sanchosimmy/Wireless-Control/Documentation/latex/globalvariable_8h__incl.pdf

C:/Users/Akshay/workspace
_v6_0/Wireless_Control
/globalvariable.h
stdbool.h | stdint.h
