sanchosimmy/Wireless-Control/Documentation/latex/input_8h__dep__incl.pdf

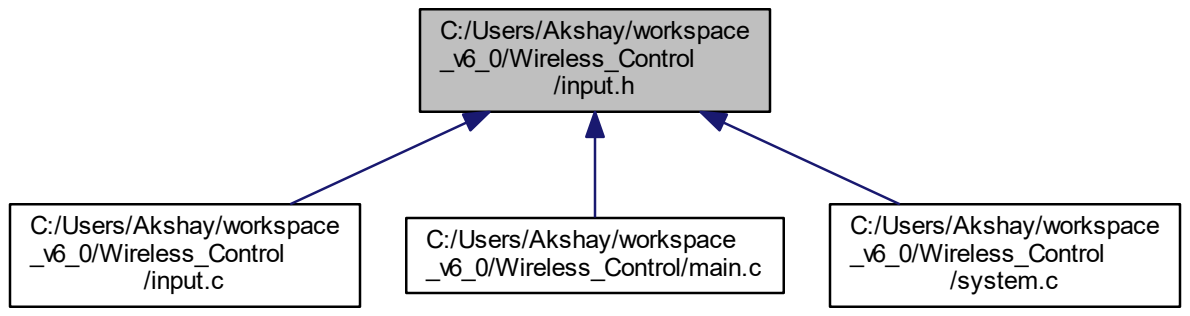
[picture p19: figure]
C:/Users/Akshay/workspace _v6_0/Wireless_Control /input.h; C:/Users/Akshay/workspace _v6_0/Wireless_Control /input.c; C:/Users/Akshay/workspace _v6_0/Wireless_Control/main.c; C:/Users/Akshay/workspace _v6_0/Wireless_Control /system.c
