sanchosimmy/Wireless-Control/Documentation/latex/input_8h__incl.pdf

C:/Users/Akshay/workspace
_v6_0/Wireless_Control
/input.h

stdint.h
