sanchosimmy/Wireless-Control/Documentation/latex/led_8h__dep__incl.pdf

C:/Users/Akshay/workspace
_v6_0/Wireless_Control/led.h

C:/Users/Akshay/workspace
_v6_0/Wireless_Control/led.c

C:/Users/Akshay/workspace
_v6_0/Wireless_Control/main.c
