sanchosimmy/Wireless-Control/Documentation/latex/pinmap_8h__dep__incl.pdf

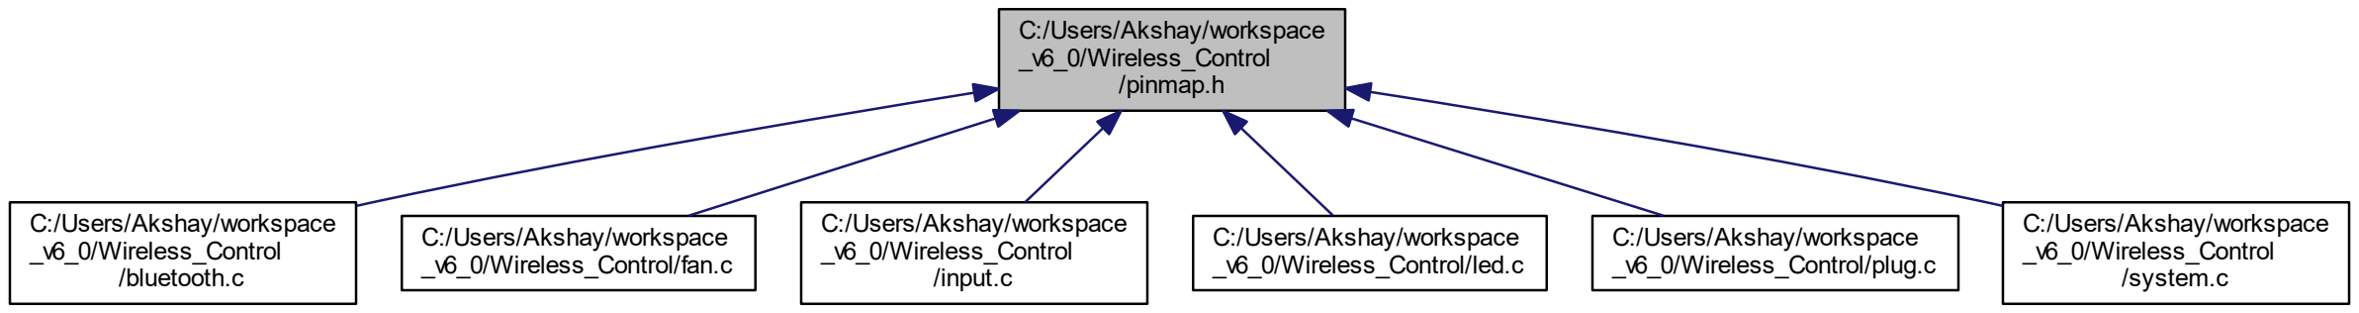
[picture p20: figure]
C:/Users/Akshay/workspace _v6_0/Wireless_Control /pinmap.h; C:/Users/Akshay/workspace _v6_0/Wireless_Control /bluetooth.c; C:/Users/Akshay/workspace _v6_0/Wireless_Control/fan.c; C:/Users/Akshay/workspace _v6_0/Wireless_Control /input.c; C:/Users/Akshay/workspace _v6_0/Wireless_Control/led.c; C:/Users/Akshay/workspace _v6_0/Wireless_Control/plug.c; C:/Users/Akshay/workspace _v6_0/Wireless_Control /system.c
