sanchosimmy/Wireless-Control/Documentation/latex/pinmap_8h__incl.pdf

C:/Users/Akshay/workspace
_v6_0/Wireless_Control
/pinmap.h
stdint.h | stdbool.h | driverlib/gpio.h | driverlib/pin_map.h
