sanchosimmy/Wireless-Control/Documentation/latex/plug_8c__incl.pdf

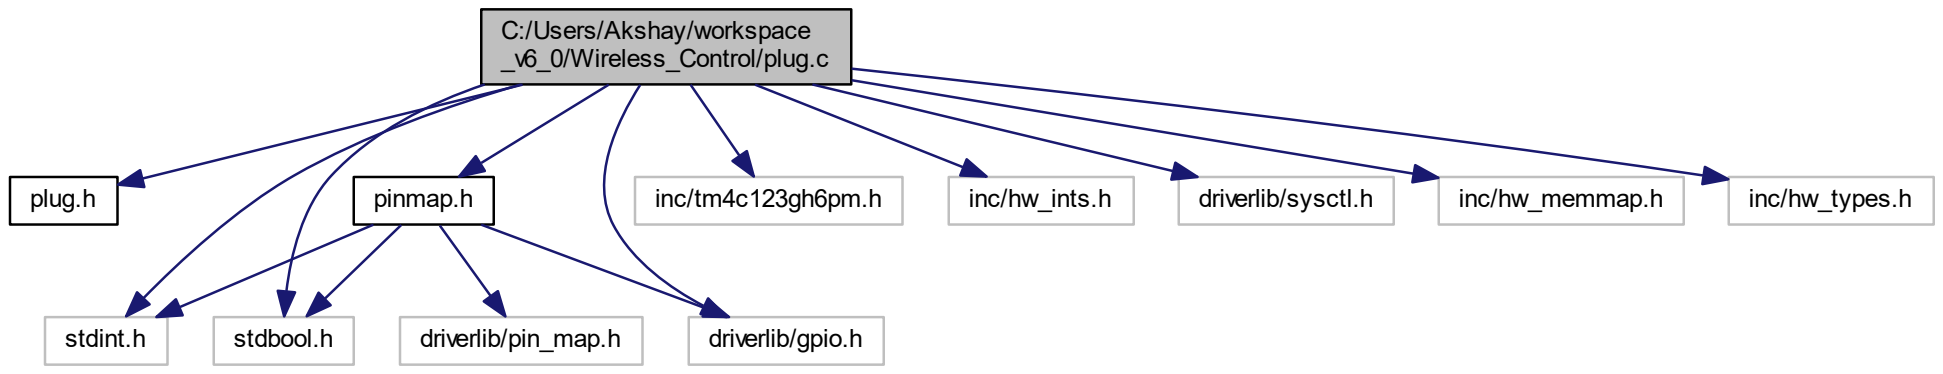
[picture p21: figure]
C:/Users/Akshay/workspace _v6_0/Wireless_Control/plug.c; plug.h; stdint.h; stdbool.h; inc/tm4c123gh6pm.h; inc/hw_ints.h; driverlib/gpio.h; pinmap.h; driverlib/sysctl.h; inc/hw_memmap.h; inc/hw_types.h; driverlib/pin_map.h
