sanchosimmy/Wireless-Control/Documentation/latex/plug_8h__dep__incl.pdf

C:/Users/Akshay/workspace
_v6_0/Wireless_Control/plug.h

C:/Users/Akshay/workspace
_v6_0/Wireless_Control/main.c

C:/Users/Akshay/workspace
_v6_0/Wireless_Control/plug.c
