sanchosimmy/Wireless-Control/Documentation/latex/system_8h__incl.pdf

C:/Users/Akshay/workspace
_v6_0/Wireless_Control
/system.h

stdint.h
