sanchosimmy/Wireless-Control/Hardwear_PCB/bottom_fan - Copy.png

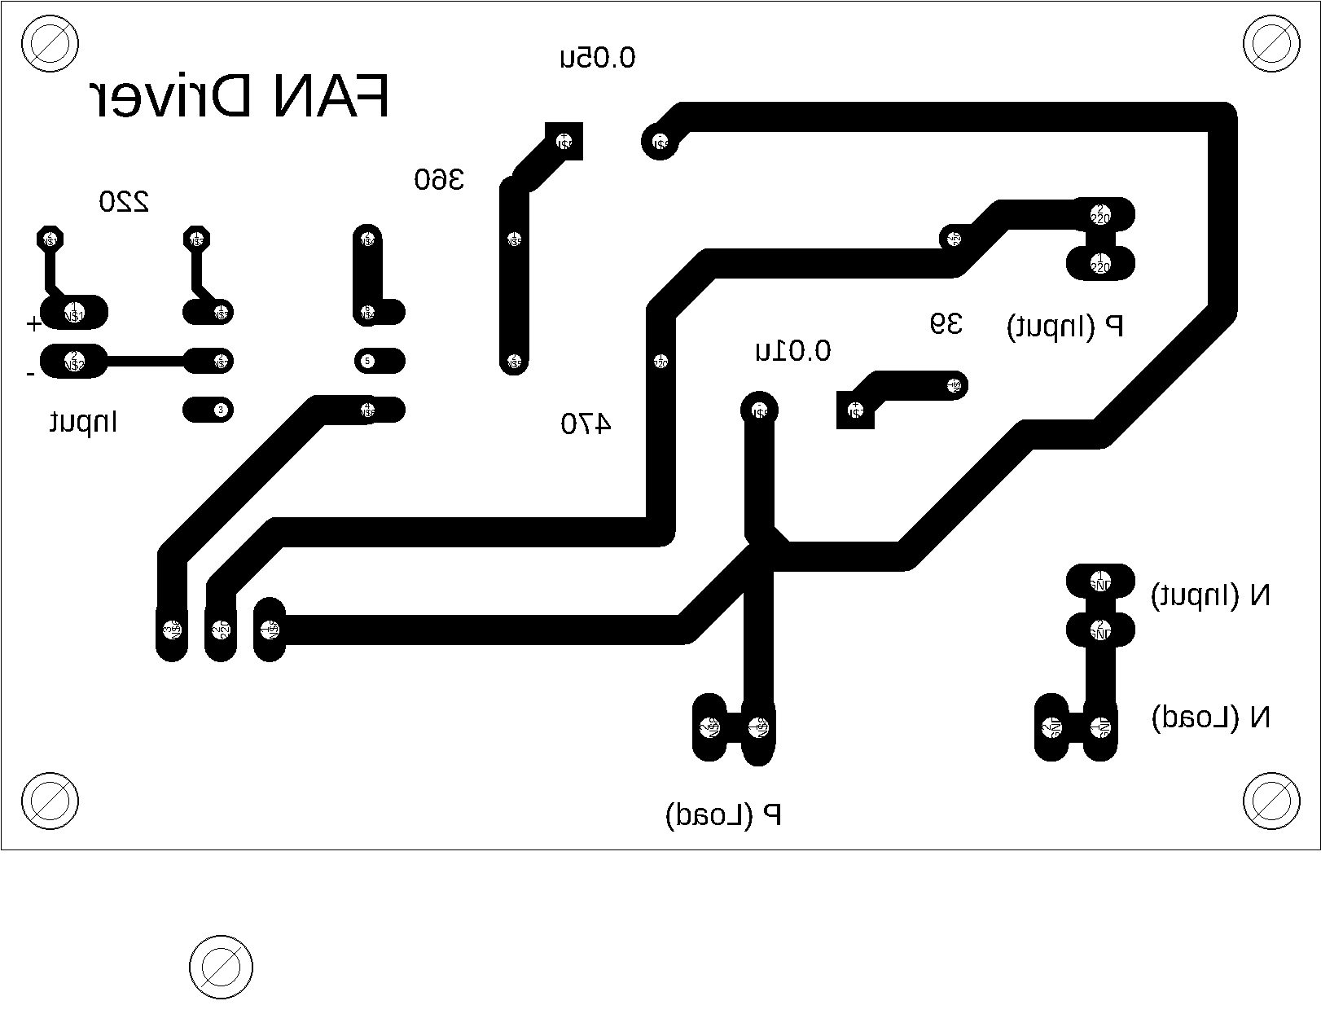
Hardwear_PCB/bottom_fan - Copy.png
