sanchosimmy/Wireless-Control/Hardwear_PCB/bottom_led - Copy.png

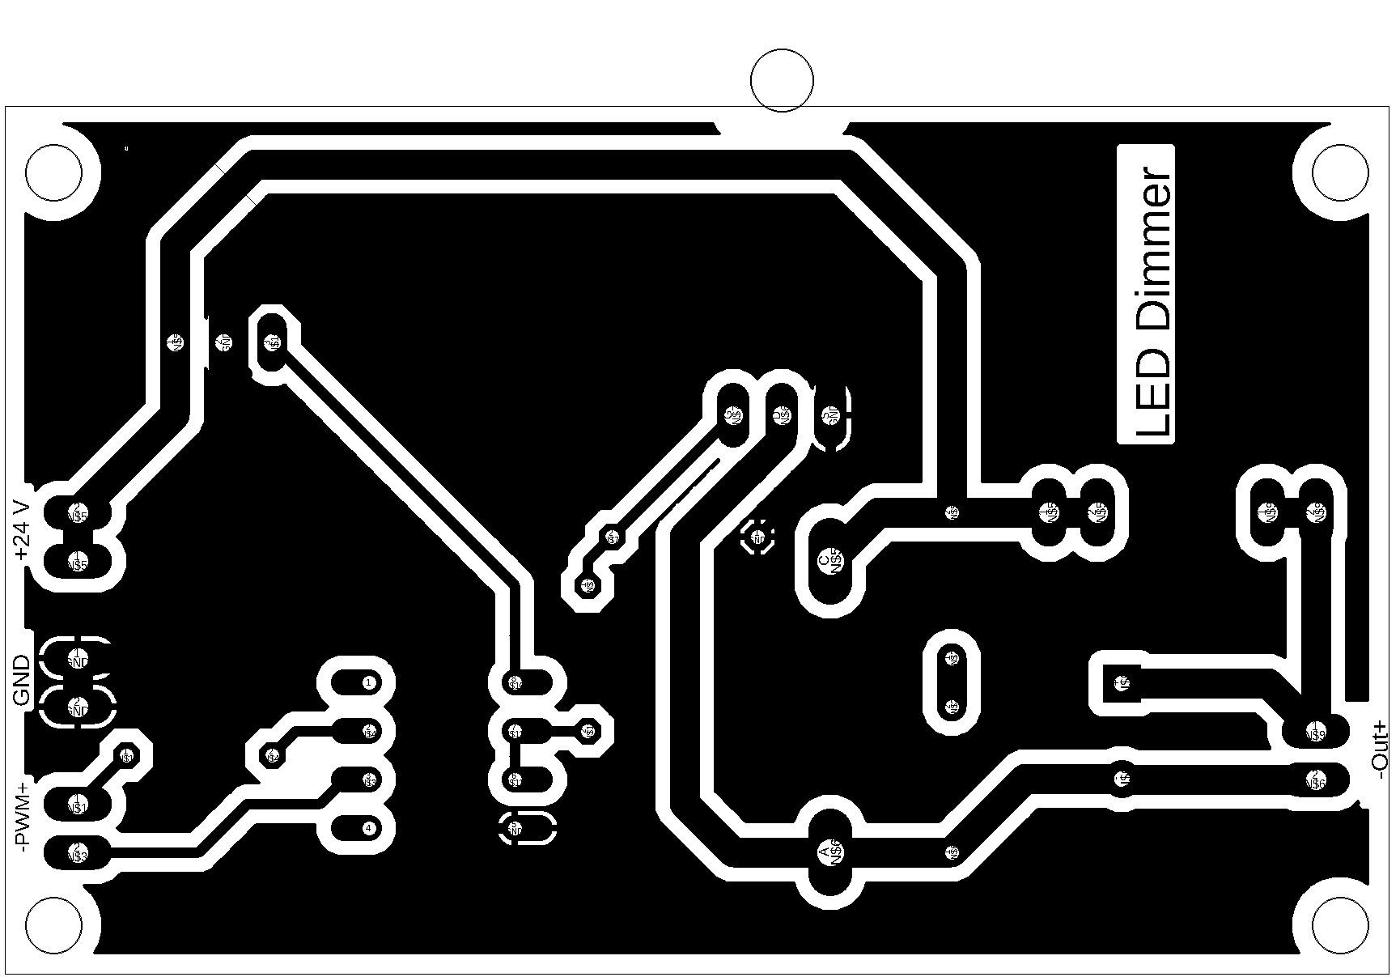
Hardwear_PCB/bottom_led - Copy.png
