sanchosimmy/Wireless-Control/Hardwear_PCB/Inverted/bottom_fan.png

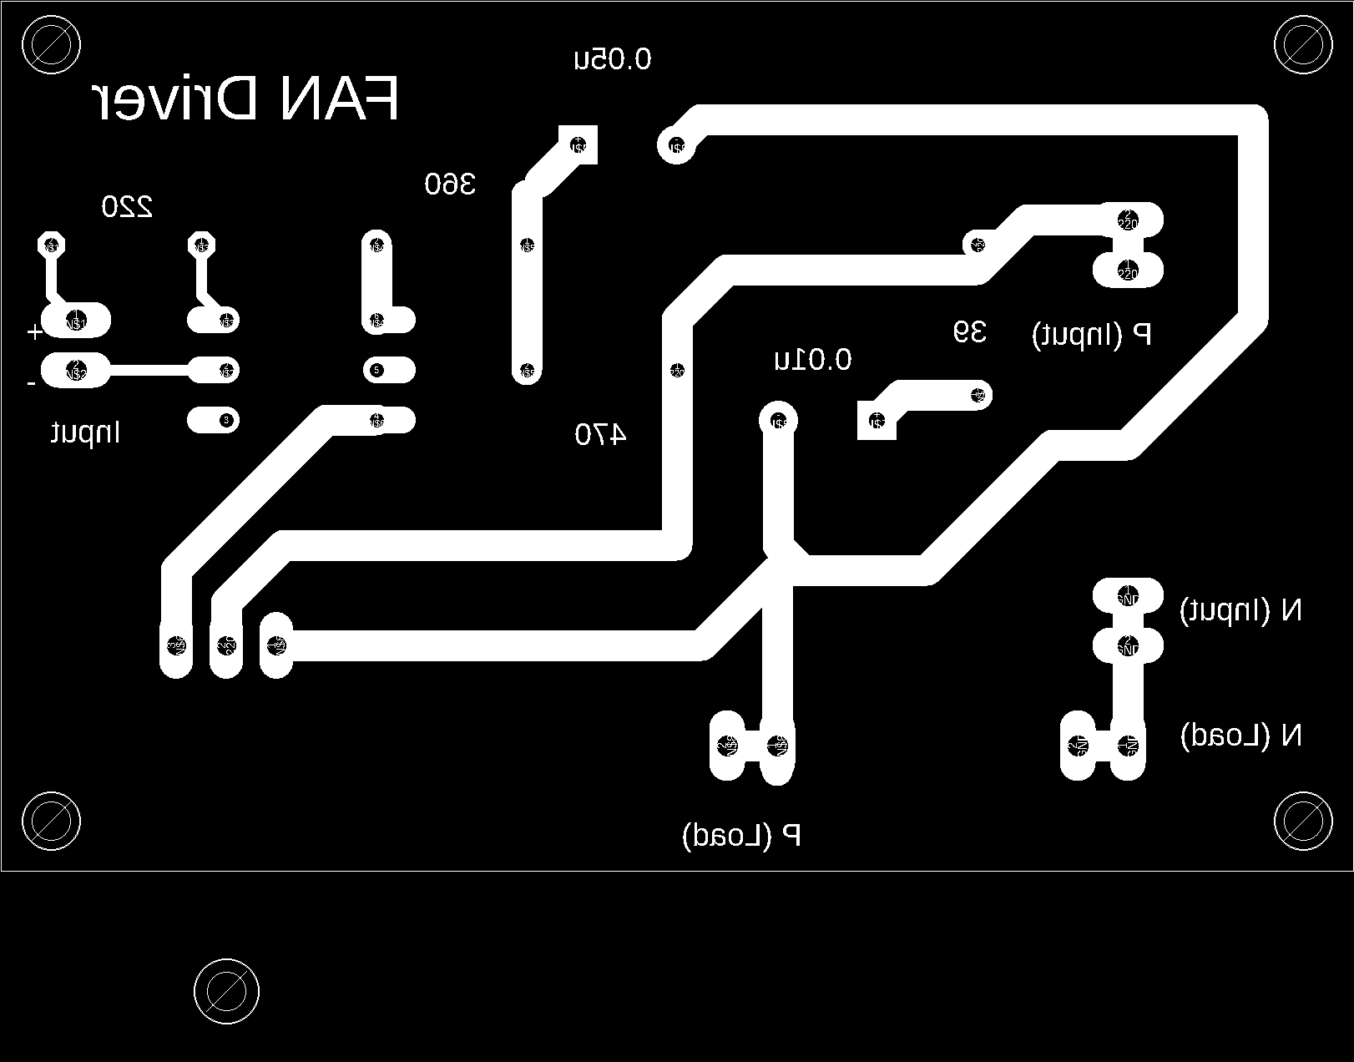
Hardwear_PCB/Inverted/bottom_fan.png
