sanchosimmy/Wireless-Control/Hardwear_PCB/Inverted/bottom_led.png

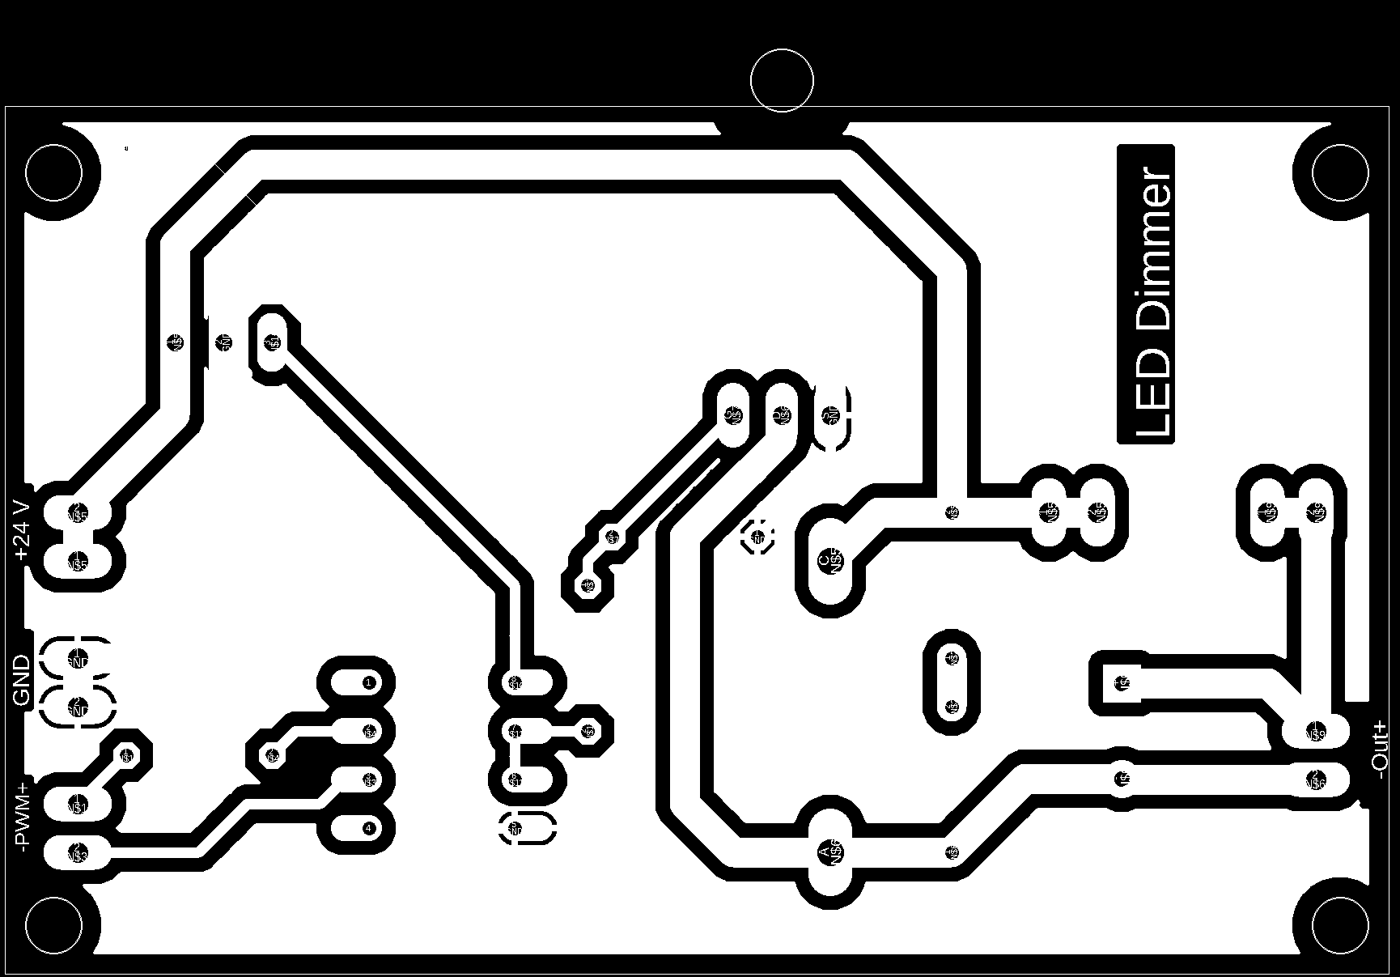
Hardwear_PCB/Inverted/bottom_led.png
