sanchosimmy/Wireless-Control/Hardwear_PCB/Inverted/main_bot.png

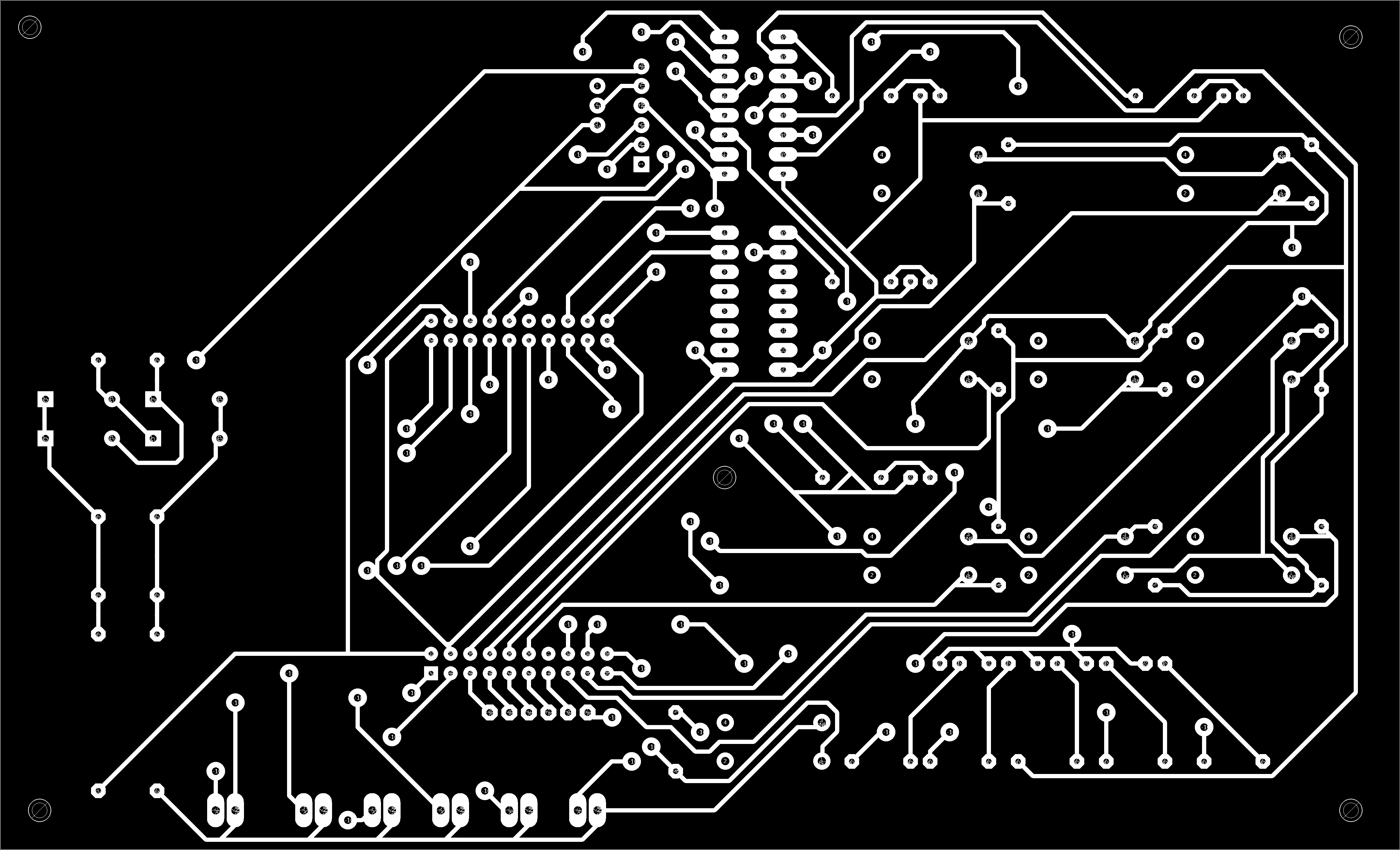
Hardwear_PCB/Inverted/main_bot.png
