sanchosimmy/Wireless-Control/Hardwear_PCB/Inverted/main_top.png

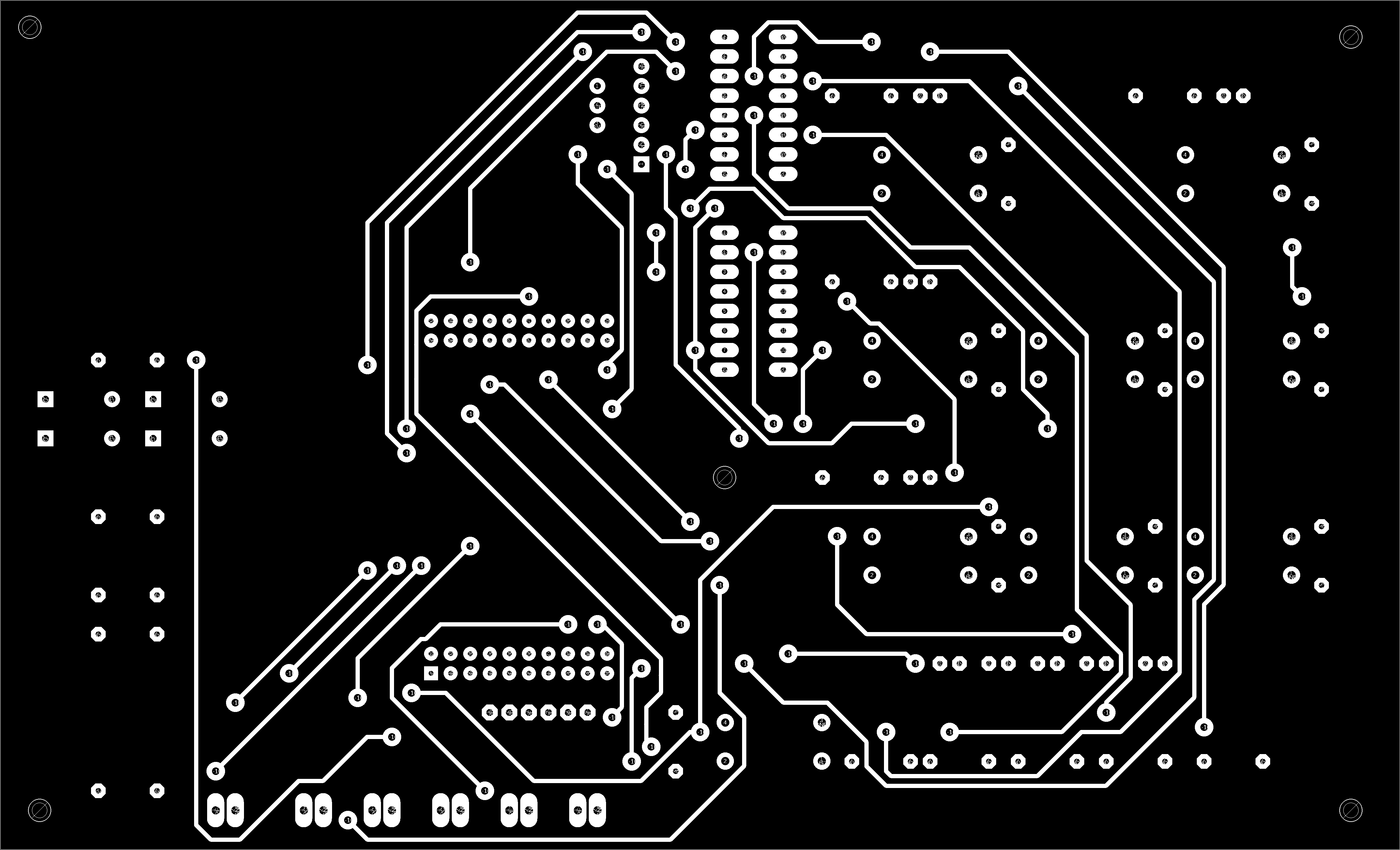
Hardwear_PCB/Inverted/main_top.png
