sanchosimmy/Wireless-Control/Hardwear_PCB/main_bot.png

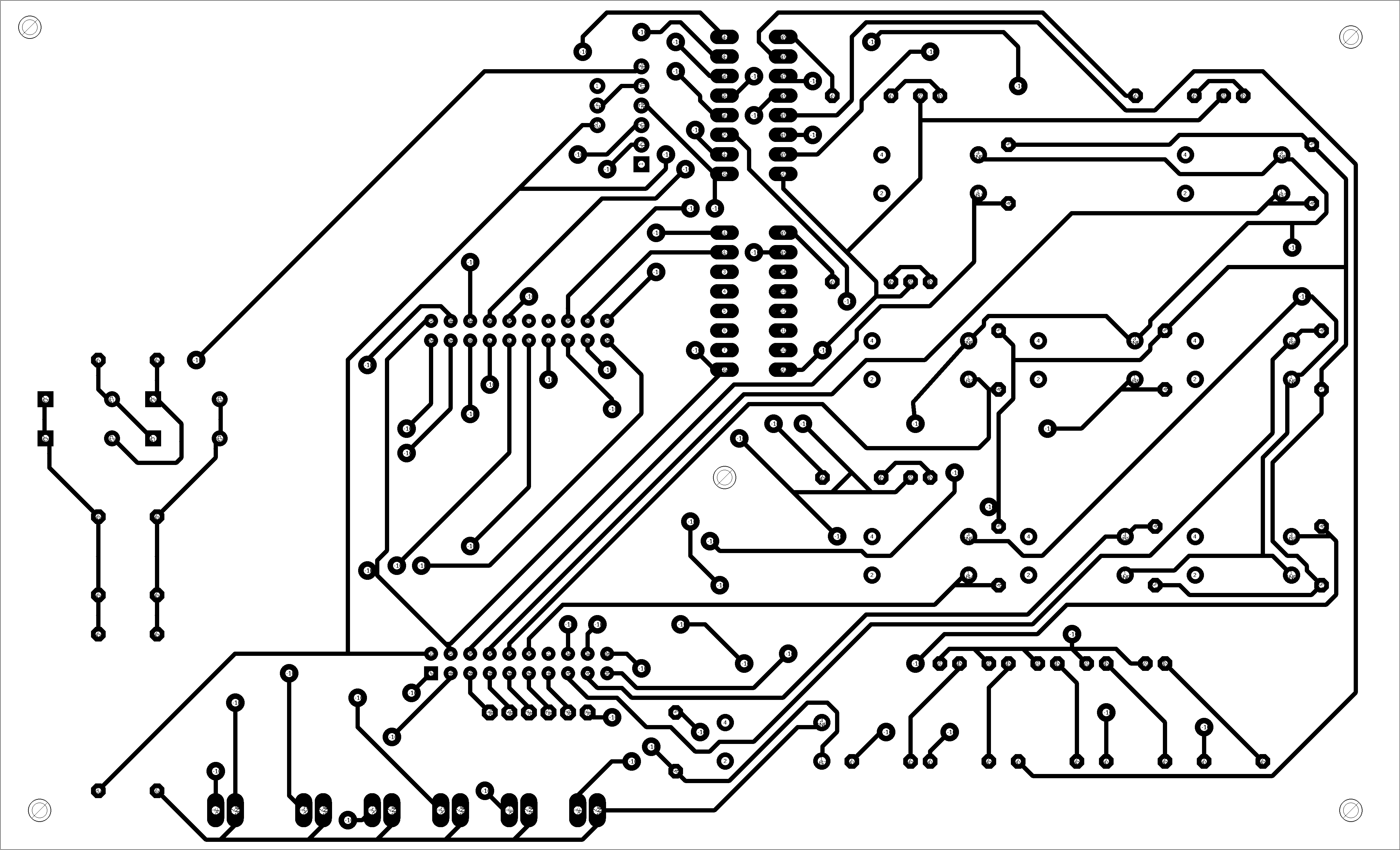
Hardwear_PCB/main_bot.png
