sanchosimmy/Wireless-Control/Hardwear_PCB/main_top.png

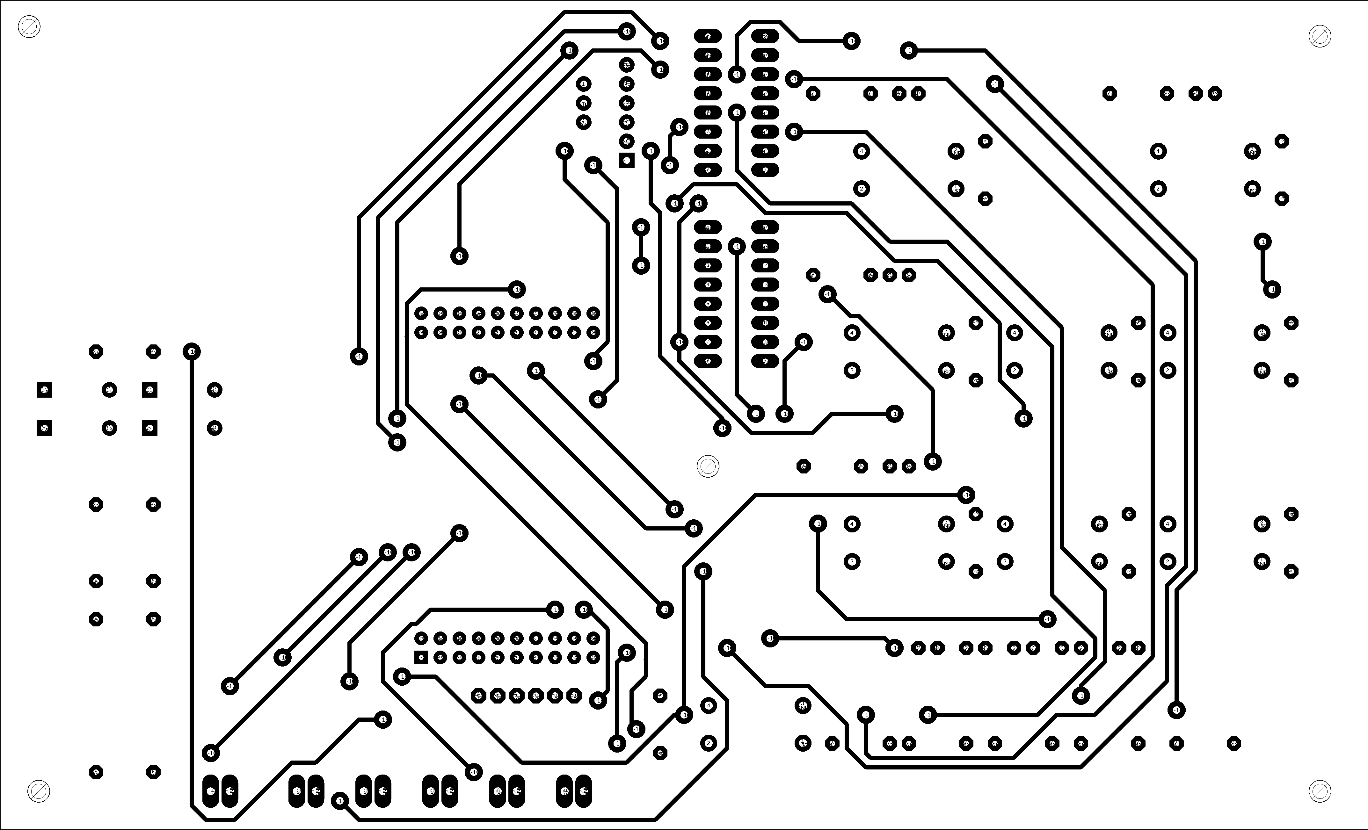
Hardwear_PCB/main_top.png
