sanchosimmy/Wireless-Control/Documentation/latex/led_8c__incl.pdf

C:/Users/Akshay/workspace
_v6_0/Wireless_Control/led.c
