sanchosimmy/Wireless-Control/Documentation/latex/main_8c__incl.pdf

C:/Users/Akshay/workspace
_v6_0/Wireless_Control/main.c
