sanchosimmy/Wireless-Control/commonheader.h

/**
 * \file commonheader.h
 * \ingroup WiControl
 * \brief Collection of header files.
 *
 * HAL: Hardware abstraction layer.
 * Almost all header file of uC tm4c123gh6pm required to complete this project.
 * \note Add it to source file of project.
 * \author Akshay Pampatwar
 * \version 0.0
 * \date 9th April 2020
 */

#ifndef COMMONHEADER_H_
#define COMMONHEADER_H_

#include <stdio.h>
#include <stdint.h>
#include <stdbool.h>
#include "inc/tm4c123gh6pm.h"
//#include "inc/hw_ints.h"
#include "inc/hw_memmap.h"
#include "inc/hw_types.h"
#include "inc/hw_ssi.h"
#include "driverlib/sysctl.h"
#include "driverlib/interrupt.h"
#include "driverlib/gpio.h"
#include "driverlib/timer.h"
#include "driverlib/systick.h"
#include "driverlib/adc.h"
#include "driverlib/debug.h"
#include <time.h>
#include <inc/hw_gpio.h>
#include "driverlib/ssi.h"		// SP
#include "driverlib/pin_map.h"
//#include "globalvariable.h"
#endif /* COMMONHEADER_H_ */
